ts-manuel/Nixie-Alarm-Clock/ltspice/DAC Filter/DAC Filter.asc

C1: cap; 1n
R1: res; 47k
R2: res; 4.7k
U1: UniversalOpamp
V1: voltage; 2.5
V2: voltage; 2.5
V3: voltage; SINE(0 2 1k); AC 1
Named nets: 0, VCC, VEE, OUT
;tran 10m
.ac dec 100 1 10Meg
