ts-manuel/Nixie-Alarm-Clock/ltspice/Rectifier/Rectifier.asc

C1: cap; 4400µ
D1: diode
D2: diode
D3: diode
D4: diode
I1: current; 1.1
V1: voltage; SINE(0 16 50)
Named nets: 0, VDC
.tran 100m
