ts-manuel/Nixie-Alarm-Clock/ltspice/B+ Boost MC34063/B+ Boost MC34063.asc

C1: cap; 400n
C2: cap; 33µ; Rser=45m
C3: cap; 33µ; Rser=45m
C4: cap; 1n
C5: cap; 480p
C6: cap; 200n
D1: diode; RF1501NS3S
D2: diode; 1N4148
I1: current; PULSE(10m 40m 5m 0 0 5m)
L1: ind; 82µ; Ipk=4 Rser=0.14
M1: nmos; Si4490DY
Q1: pnp; 2N3906
R1: res; 0.075
R2: res; 680k
R3: res; 4.7k
R4: res; 4.7k
R5: res; 4.7k
R6: res; 10
R7: res; 2.66
U1: mc34063
V1: voltage; 14
Named nets: 0
.tran 0 10m 0 100n uic
.inc MC34063.lib
.options Gmin=1e-9  method=Gear
