ts-manuel/Nixie-Alarm-Clock/ltspice/B+ Boost/B+ Boost.asc

C1: cap; 680n
C2: cap; 47µ
D1: diode; RF1501NS3S
I1: current; 40m
L1: ind; 100µ
R1: res; 2.66
R2: res; 680k
R3: res; 4.7k
S1: sw; MYSW
V1: voltage; 14
V2: voltage; PULSE(0 1 0 10n 10n 16u 20u)
Named nets: 0
.model MYSW SW(Ron=1 Roff=1Meg Vt=.5 Vh=-.4)
.tran 10m
