ts-manuel/Nixie-Alarm-Clock/ltspice/B+ Flyback DCM LTC3803/B+ Flyback DCM LTC3803.asc

C1: cap; 1n
C2: cap; 1n
C3: cap; 1n
C4: cap; 1n
C5: cap; 47µ
C6: cap; 400n
C8: cap; 400n
C9: cap; 1µ; IC=9
C10: cap; 1n
D1: diode; RFN2LAM6S
D3: diode; RFN2LAM6S
I2: current; PULSE(20m 40m 2m 0.01m 0.01m 2m)
L1: ind2; 16.7µ; Cpar=1p
L2: ind2; 150µ; Cpar=2p
L3: ind; 0.22µ
Q1: pnp; 2N3906
Q2: nmos; BSC320N20NS3
R1: res; 0.023
R2: res; 0.357
R3: res; 100
R4: res; 4.7k
R5: res; {POT * D}
R6: res; 10
R7: res; 0.033
R8: res; 470
R9: res; 680K
R10: res; 4.7K
R11: res; 47K
R12: res; 470
R13: res; 4.7k
R14: res; 4.7k
R15: res; {POT * (1-D)}
R16: res; 4.7k
R17: res; 4.7k
R18: res; 2.5
R19: res; 0.1
R20: res; 4.7k
U1: LTC3803
V1: voltage; PULSE(0 3 1m 0 0 2m)
V2: voltage; 14
Named nets: 0, IN
.tran 0 4.51m 0.5m 100n startup
K1 L1 L2 1
.param POT=56k
.param D=0.2
.step param D list 0.01 0.5 0.99
.model MYSW SW(Ron=0.01 Roff=1Meg Vt=.5 Vh=-.4)
