ts-manuel/Nixie-Alarm-Clock/ltspice/B+ Flyback/B+ Flyback.asc

C1: cap; 680n; IC=18
C2: cap; 8µ; IC=12
C3: cap; 100n
C4: cap; 220p
C5: cap; 220p
C6: cap; 100n
C7: cap; 220p; IC=180
D1: diode; RFN5TF6S
D2: diode; 1N4148
I1: current; 20m
R1: res; 0.2
R2: res; 680k
R3: res; 4.7k
R4: res; 4.7k
R5: res; 10k
R6: res; 1k
T1: 750311681
U1: mc34063
V1: voltage; 12
Named nets: 0
.tran 0 2m 1u 100n uic
.inc MC34063.lib
.options Gmin=1e-9  method=Gear
