ts-manuel/Nixie-Alarm-Clock/ltspice/Constant Current Anode Switching/Constant Current Anode Switching.asc

D1: zener; UDZLV120
D2: zener; UDZLV120
D3: zener; UDZLV120
D4: zener; UDZLV120
D5: zener; UDZLV120
D6: zener; UDZLV120
D7: zener; UDZLV120
D8: zener; UDZLV120
Q1: npn; 2SCR346P
Q2: npn; 2SCR346P
Q3: pnp; 2SAR340P
Q4: pnp; 2SAR340P
Q5: pnp; 2SAR340P
Q6: npn; 2SCR346P
Q7: npn; 2SCR346P
Q8: npn; 2SCR346P
Q9: npn; 2SCR346P
Q10: pnp; 2SAR340P
Q11: pnp; 2SAR340P
Q12: pnp; 2SAR340P
Q13: pnp; 2SAR340P
Q14: npn; 2SCR346P
Q15: pnp; 2SAR340P
Q16: pnp; 2SAR340P
Q17: pnp; 2SAR340P
Q18: npn; 2SCR346P
Q19: npn; 2SCR346P
Q20: pnp; 2SAR340P
Q21: pnp; 2SAR340P
Q22: pnp; 2SAR340P
R1: res; 4.7k
R2: res; 4.7k
R3: res; 4.7k
R4: res; 4.7k
R5: res; 680k
R6: res; 680k
R7: res; 680k
R8: res; 680k
R9: res; 4.7k
R10: res; 4.7k
R11: res; 4.7k
R12: res; 4.7k
R13: res; 680k
R14: res; 47k
R15: res; 4.7k
R16: res; 680k
R17: res; 47k
R18: res; 680k
R19: res; 4.7k
R20: res; 4.7k
R21: res; 4.7k
R22: res; 680k
R23: res; 22k
R24: res; {POT * D}
R25: res; {POT * (1- D )}
R26: res; 680k
R27: res; 680k
R28: res; 680k
R29: res; 680k
R30: res; 680k
R31: res; 4.7k
R32: res; 4.7k
R33: res; 4.7k
R34: res; 4.7k
R35: res; 680k
R36: res; 680k
R37: res; 680k
R38: res; 680k
V1: voltage; 180
V2: voltage; 3
V3: voltage; 3
Named nets: 0, B+, VDD, SEL
.tran 0 10m 1m
.param D=0.01
.step param D list 0.01 .5 .99
.param POT=56k
