ts-manuel/Nixie-Alarm-Clock/mplabx/NixieAlarmClock.X/src/global.c

/* 
 * File:   global.c
 * Author: ts-manuel
 *
 * This file contains the declaration for all global variables used to transfer
 * information between modules
 */

#include "rtcc.h"
#include "config.h"
#include "tasks/display.h"
#include "tasks/alarm.h"
#include "tasks/player.h"

DispBuffer_t display;

AlarmSlot_t alarmSlots[_ALARM_SLOT_COUNT];
bool flagTriggerAlarm;

bcdTime_t rtcTime;

PlayerCtrl_t playerCtrl;
int8_t playerVolume;
